falkm1980/IoT-Testboard/weatherConfig.py

#!/usr/bin/env python2
# -*- coding: utf-8 -*-
"""
Created on Sun Dec 11 20:31:30 2016

@author: Markus
"""

#from tftSimulator import tftSimulator as display
from ili9341AdafruitWrapper import ili9341AdafruitWrapper as display
